MarceloPesse/Demeter-SoilMoistureMeter/Software/si_demeter/themeforest-2834580-supr-responsive-admin-template/documentation/assets/images/image_5.jpg

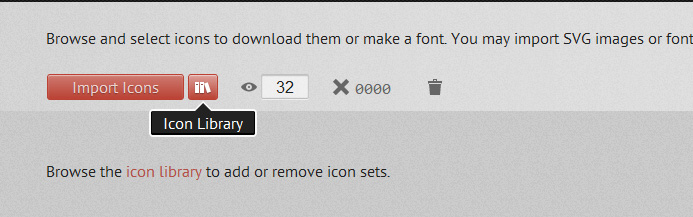
Software/si_demeter/themeforest-2834580-supr-responsive-admin-template/documentation/assets/images/image_5.jpg
